kd8bxp/Tandy102-SD-Card-Drive-with-WiFi-Modem/max232-board-250x250.jpg

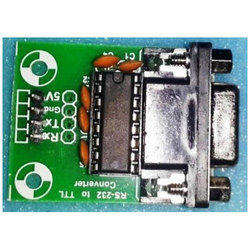
max232-board-250x250.jpg
