kd8bxp/Tandy102-SD-Card-Drive-with-WiFi-Modem/Pictures/2019-06-08 01.26.08.jpg

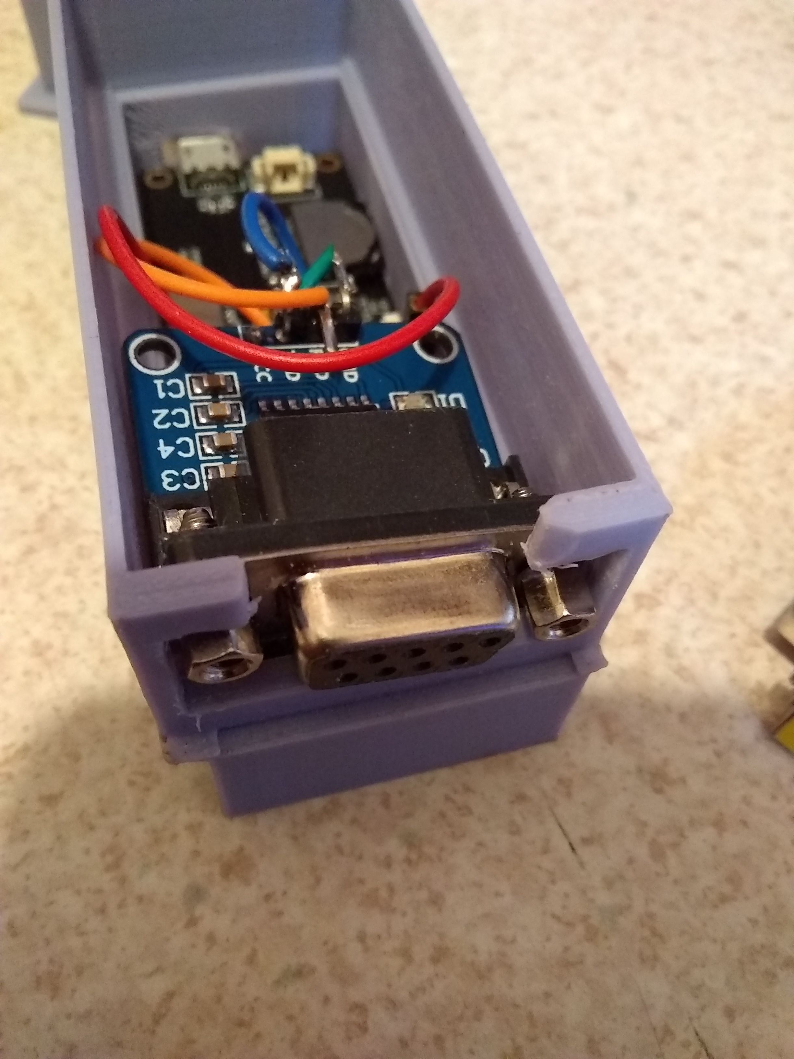
Pictures/2019-06-08 01.26.08.jpg
