kd8bxp/Tandy102-SD-Card-Drive-with-WiFi-Modem/Pictures/IMG_20190526_141857550.jpg

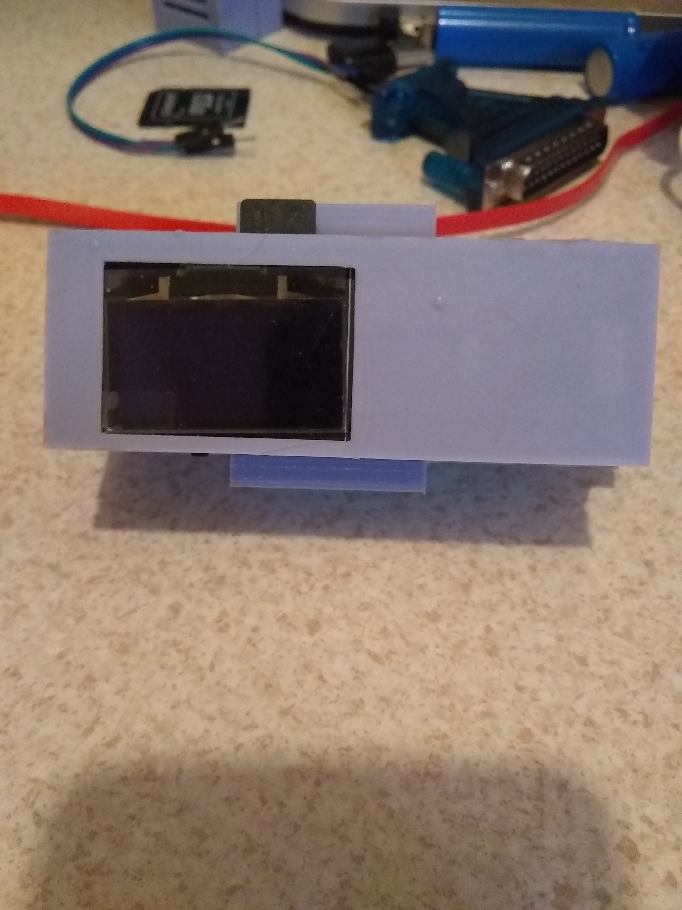
Pictures/IMG_20190526_141857550.jpg
