kd8bxp/Tandy102-SD-Card-Drive-with-WiFi-Modem/Pictures/IMG_20190526_142610006.jpg

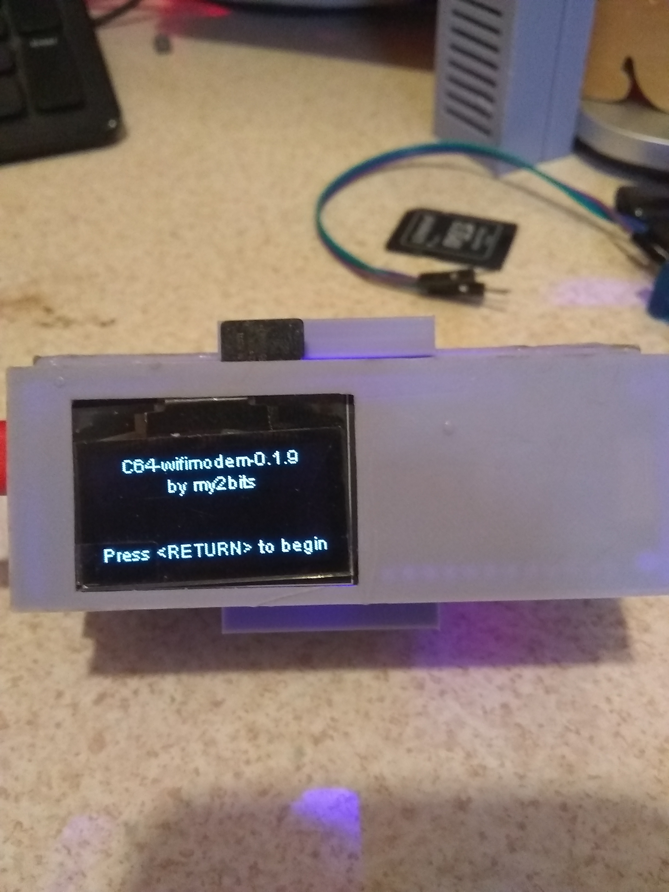
Pictures/IMG_20190526_142610006.jpg
