kd8bxp/Tandy102-SD-Card-Drive-with-WiFi-Modem/Pictures/IMG_20190526_142613378.jpg

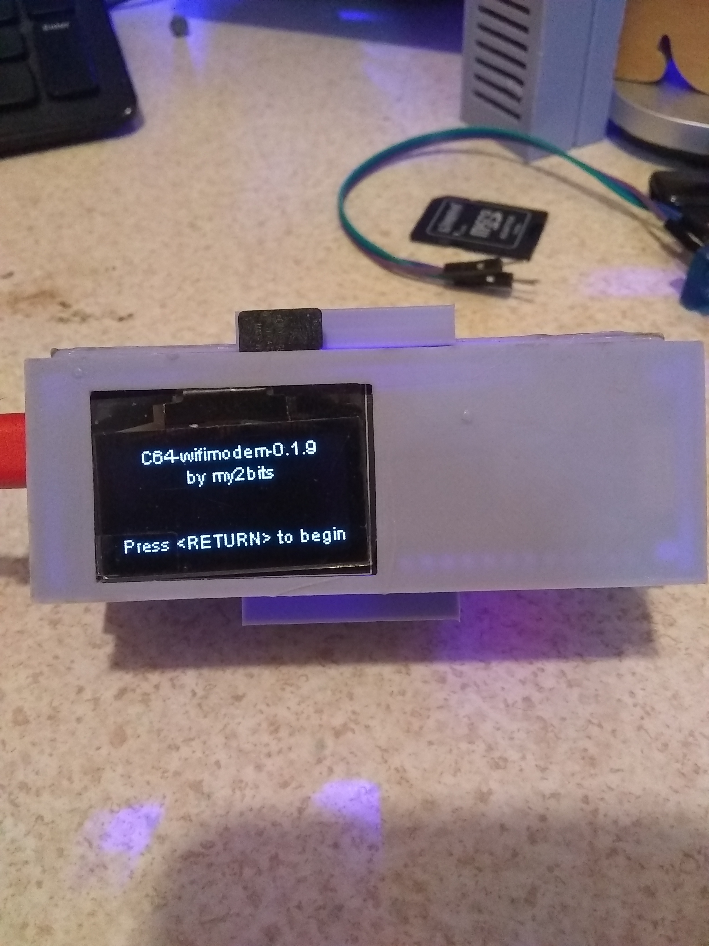
Pictures/IMG_20190526_142613378.jpg
