kd8bxp/Tandy102-SD-Card-Drive-with-WiFi-Modem/Pictures/IMG_20190527_001857808.jpg

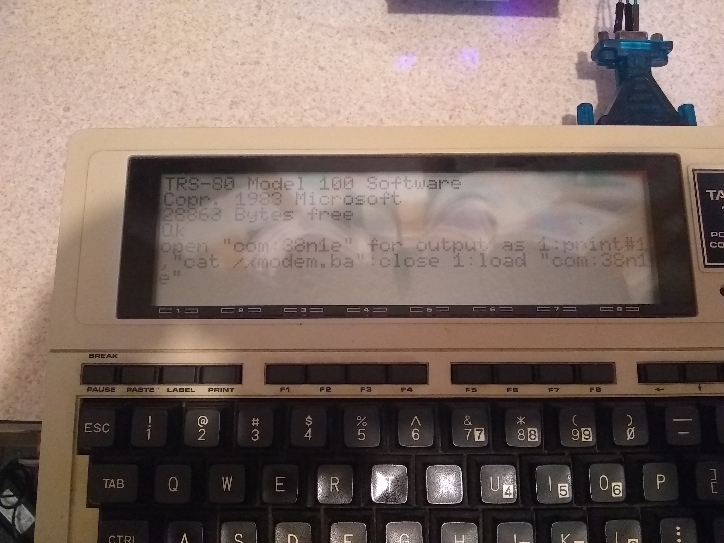
Pictures/IMG_20190527_001857808.jpg
