kd8bxp/Tandy102-SD-Card-Drive-with-WiFi-Modem/Pictures/IMG_20190527_001904478.jpg

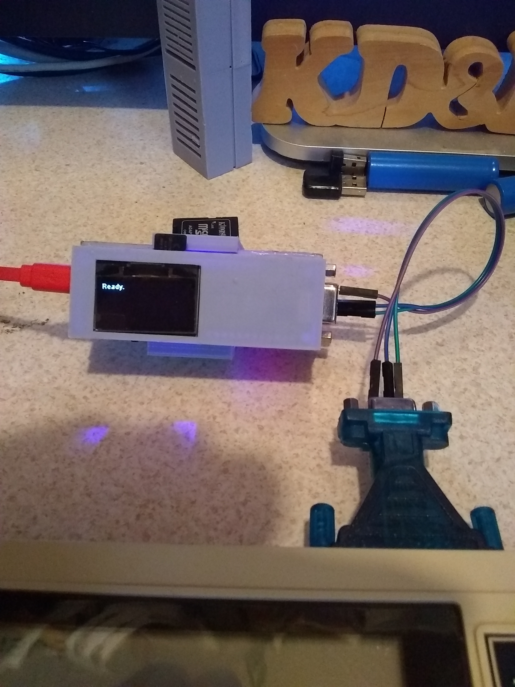
Pictures/IMG_20190527_001904478.jpg
