kd8bxp/Tandy102-SD-Card-Drive-with-WiFi-Modem/Pictures/IMG_20190528_185738126.jpg

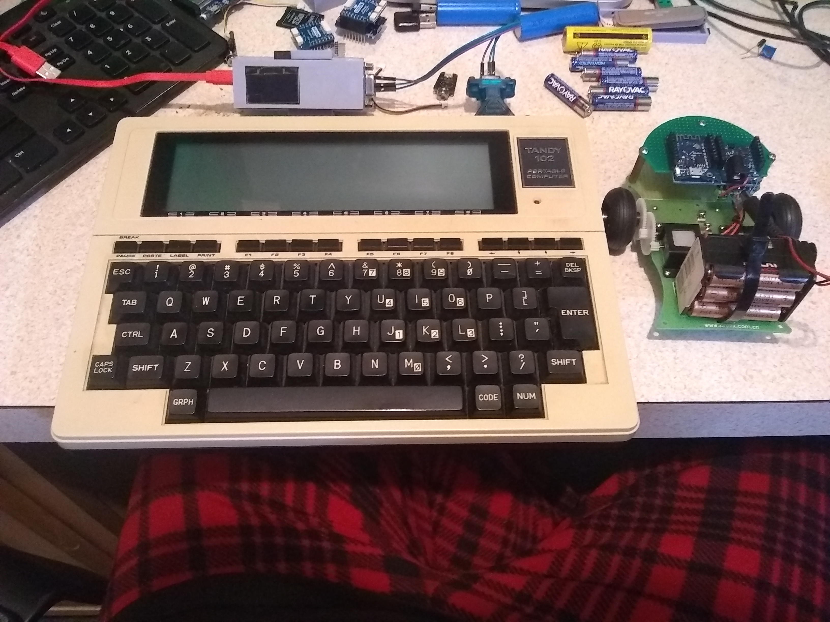
Pictures/IMG_20190528_185738126.jpg
