kd8bxp/Tandy102-SD-Card-Drive-with-WiFi-Modem/Pictures/IMG_20190528_185742167.jpg

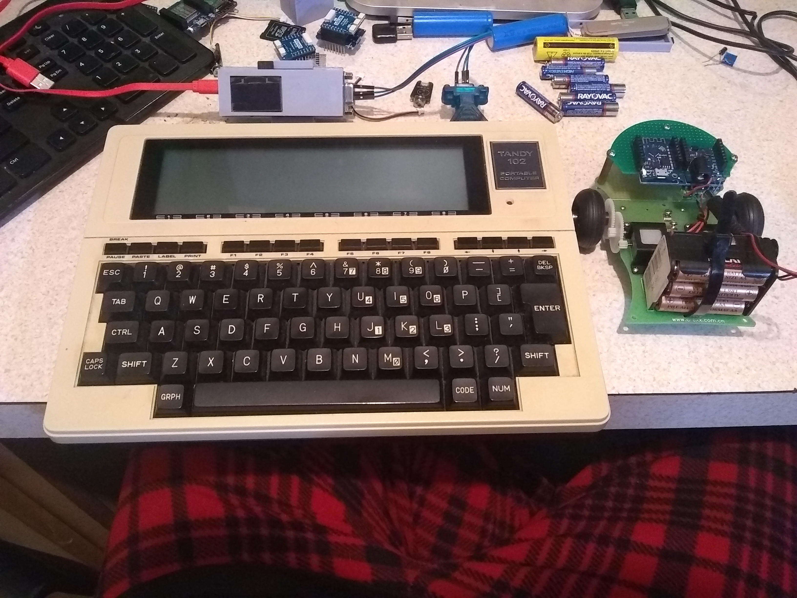
Pictures/IMG_20190528_185742167.jpg
