kd8bxp/Tandy102-SD-Card-Drive-with-WiFi-Modem/Pictures/IMG_20190605_004237450.jpg

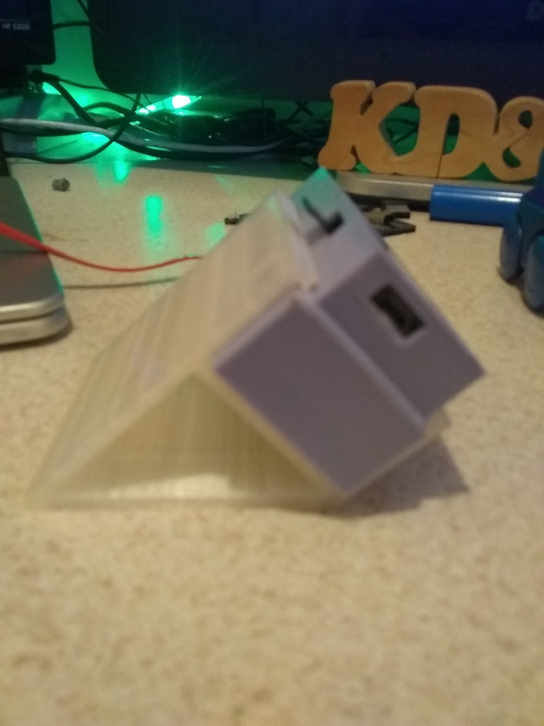
Pictures/IMG_20190605_004237450.jpg
