kd8bxp/Tandy102-SD-Card-Drive-with-WiFi-Modem/ttgo_teight.jpg

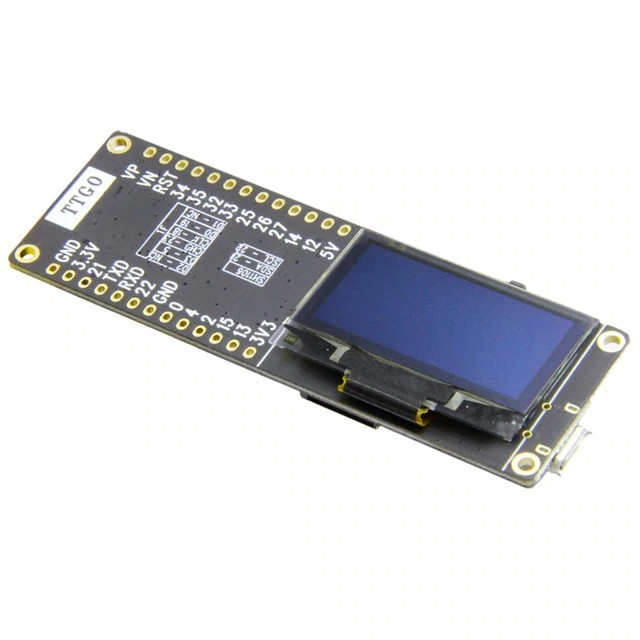
ttgo_teight.jpg
