kd8bxp/Tandy102-SD-Card-Drive-with-WiFi-Modem/Tandy_102_WiFi_SD_card/credit.h

/*
 * Tandy 102 WiFi SD card drive 
 * 
 * Ported to the ESP32 (TTGO T-Eight Board) by LeRoy Miller, May 2019
 * 
 * based on the following projects: 
 * 
 *  **************************************************************************
 *  **** MyTeSed: T100 SD Card Reader for Arduino Nano and SD Card Reader ****
 *  **** Should work with other rs232 enabled PC's in text mode transfers ****
 *  **** Xmodem for bin files, but this is not working on the Tandy ATM.  ****
 *  **************************************************************************
 *  ** David Stephenson 2017-10-11  **
 *  ** Version 0.03                 **
 *  **********************************
 *  For more information about this project see:
 *  https://www.zx81keyboardadventure.com/2017/08/model-100-micro-sd-card-reader-mytesed.html
 *  https://youtu.be/7AtsHzl9WMc
 *  
 *  And the C64-WiFiModem project which was based on serveral other projects as well.
 *  https://github.com/DrZingo/c64-wifimodem
 *  
   C64-WiFiModem - (c) 2017 my2bits <markus at borgelin.org>
   changes here
   Built hardware based on ESP-12, 3.3V-reg and level shifters.
   Tidy up help, and categorizing
   Added automatic firmware check at startup
   Corrected connectWifi() link check
   Changed MAX_CMD_LENGTH to actual FIFO buffer size
   Fixed help-bug in 9600+ baud
   Corrected setBaudRate(), bauds[] array and sizeof, to error out correct
   Adjusted pinouts for my needs
   Adjusted default servers
   Added modem restart command
   Added OLED display with information
   Added OTA Update
   Added scan for wifi
   Some fixes to Pin polarity, does not work as expected though. Fixes welcome
   Probably added more stuff I forgot to write here.
   Thanks to Paul Richards and Jussi Salin for source code.

   based on
   WiFi SIXFOUR - A virtual WiFi modem based on the ESP 8266 chipset
   Copyright (C) 2016 Paul Rickards <rickards@gmail.com>
   Added EEPROM read/write, status/help pages, busy answering of incoming calls
   uses the readily available Sparkfun ESP8266 WiFi Shield which has 5v level
   shifters and 3.3v voltage regulation present-- easily connect to a C64
   https://www.sparkfun.com/products/13287

   based on
   ESP8266 based virtual modem
   Copyright (C) 2016 Jussi Salin <salinjus@gmail.com>

   https://github.com/jsalin/esp8266_modem

FTP Server based on FTPServerSample & esp8266FTPServer by nailbuster Oct 2017
https://github.com/nailbuster/esp8266FTPServer
Modified by robo8080 for SD card use 2017 https://github.com/robo8080/ESP32_FTPServer_SD
Slightly Modified by LeRoy Miller, 2019 to include OLED code, and work in a menu system.

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
   You should have received a copy of the GNU General Public License
   along with this program.  If not, see <http://www.gnu.org/licenses/>.
 */

 /*
  * Changes and Additions:
  * MyTeSed Changes: (Slightly modified to work on the ESP32)
  * (May 2019)
  * Added "FILES", "KILL", and "HELP" to SD portion of code
  * Added status on the OLED as to status of SD drive load and save
  * Added xmodem status to OLED
  * Changed "FILES" and "DIR" subroutine back to a previous version that seemed to work better with my hardware
  *  - added file size back for display, plus tabs
  * Changed the filename check and extension check to also include the "/" in file name (needed for my hardware, and SD card) line 356
  *  - change/update code to check if "/" is present if not add it (this will require work)
  *  Line 323 - void OutFileTimeOut() added timeout warning display on OLED
  *  Line 385 - added the new commands that don't require a filename "FILES", "HELP"
  *  Line 402 - IF check "COPY2R" and "CAT" changed to the old method of "LOAD", but I'm not sure I needed to do this - because I missed how LINE 356 was checking the file names
  *  Line 435 added "FILES" and Line 441 added "KILL"
  *  Line 477 added "HELP" and display help on OLED (just list the commands that can be used, but doesn't tell how - simple help)
  *  void Setup added OLED code, added "Intro Screen", SD card check, checked display from Serial to OLED
  *  
  *  FTP Server Changes:
  *  (May 2019)
  *  Added Code for OLED, added code to work within the menu system.
  *  Slightly modified the SD card check, IF no card found, the ESP32 will reboot.
  *  
  *  C64-WiFi-Modem Changes and notes:
  *  (May 2019)
  *  Modified slightly to work on the ESP32.
  *  Removed some code that I believe the telnet server needed.
  *  * Telnet Server is not working, otherwise this is a reasonable port to 
  *   The ESP32 device.
  */

  /*
   * Other Notes:
   * May 2019 - There is some reduntant code currently, 
   * The 1st step to get this to work was to "merge" all the code together (more or less) as written
   * Once the code works, reducing, and making the code more efficient are the next steps
   * 
   * When running the SD Card Drive - a leading / is required in the file name otherwise it doesn't work. 
   * I plan on attempting to change this.
   *    * 
   */
